Circuit-Digest/MLX90640-Thermal-Camera/Images/PCB White BG.png

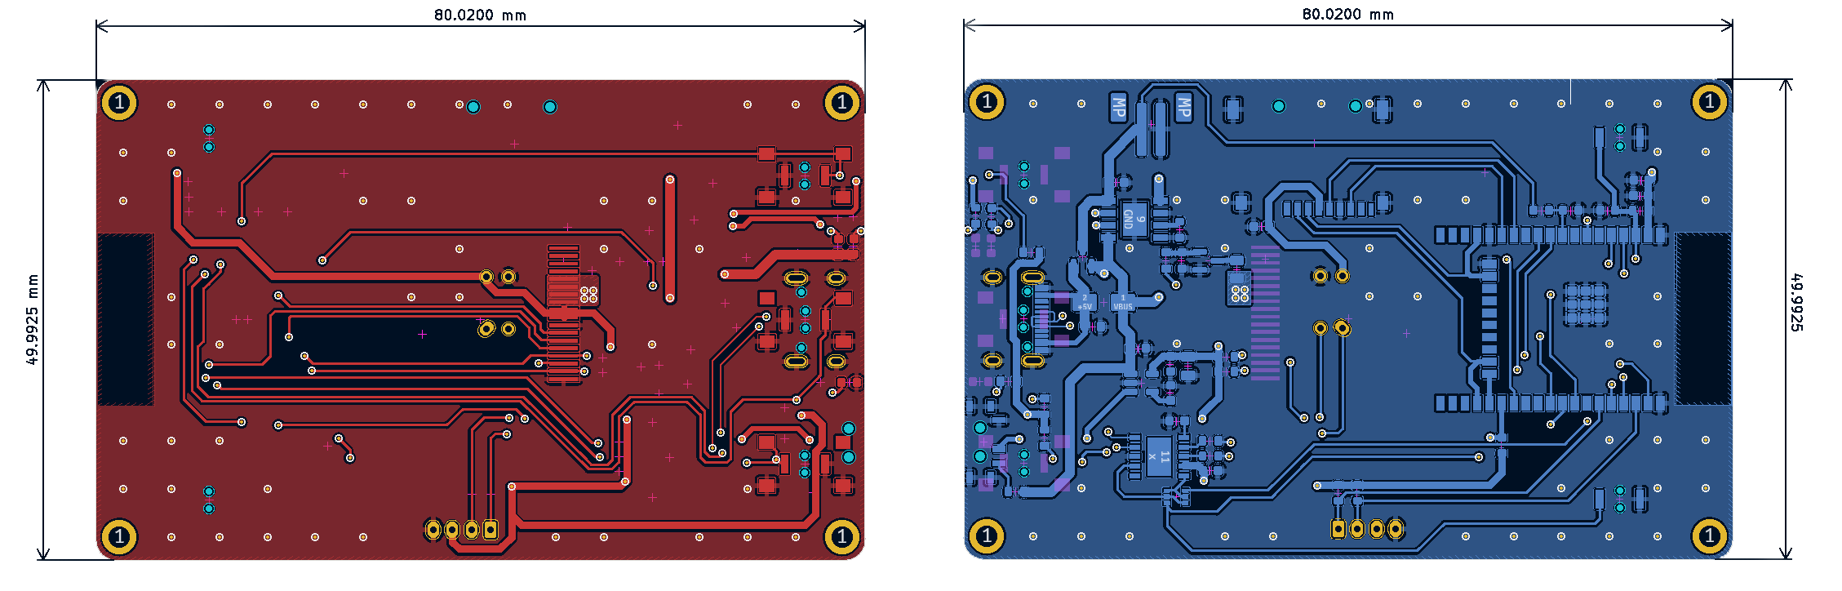
Images/PCB White BG.png
