Circuit-Digest/MLX90640-Thermal-Camera/Thermal_Camera/Error.h

/*
 * Project Name: MLX90640 Thermal Camera
 * Project Brief: Firmware for Thermal camera built around ESP32 and MLX90640
 * Author: Jobit Joseph
 * Copyright © Jobit Joseph
 * Copyright © Semicon Media Pvt Ltd
 * Copyright © Circuitdigest.com
 * 
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
 */
 //
// Error
// Data size = 30092 bytes
//
// GIF, Compression=LZW, Size: 160 x 160, 8-Bpp
// 29 frames
//
// for non-Arduino builds...
#ifndef PROGMEM
#define PROGMEM
#endif
const uint8_t Error_GIF[] PROGMEM = {
	0x47,0x49,0x46,0x38,0x39,0x61,0xa0,0x00,0xa0,0x00,0xf7,0xff,0x00,0xff,0x7c,0x80,
	0xff,0xda,0xdc,0xff,0xf2,0xf3,0xff,0xff,0xff,0xff,0xf1,0xf2,0x00,0x00,0x00,0xff,
	0xf3,0xf4,0xff,0xf4,0xf5,0xff,0xd9,0xdb,0xff,0xf0,0xf1,0xff,0xd8,0xda,0xff,0xf6,
	0xf7,0xff,0x7d,0x81,0xff,0xf7,0xf8,0xff,0xd6,0xd8,0xff,0xf5,0xf6,0xff,0xd5,0xd7,
	0xff,0xdb,0xdd,0xff,0xd7,0xd9,0xff,0xf0,0xf2,0xff,0xf7,0xf7,0xff,0xf4,0xf4,0xff,
	0xf6,0xf6,0xff,0x7a,0x7e,0xff,0xdd,0xdf,0xff,0xdc,0xde,0xff,0xf1,0xf3,0xff,0x81,
	0x85,0xff,0xf5,0xf5,0x42,0x38,0x38,0xff,0xe7,0xe9,0xff,0xa9,0xac,0xff,0xa1,0xa4,
	0xff,0x90,0x94,0xff,0x72,0x76,0xff,0xec,0xee,0xff,0x76,0x7a,0xff,0xdf,0xe1,0xff,
	0x79,0x7d,0xff,0xee,0xf0,0xff,0x6d,0x71,0xff,0x6e,0x72,0xff,0x7e,0x82,0xff,0xe1,
	0xe3,0xff,0xec,0xec,0xff,0x89,0x8d,0xff,0xde,0xe0,0xff,0xe6,0xe8,0xd1,0xb1,0xb3,
	0xff,0x74,0x78,0xff,0xad,0xb0,0xff,0x6c,0x70,0xff,0x8d,0x91,0xff,0xe0,0xe2,0xff,
	0xe6,0xe6,0xff,0xf8,0xf8,0xff,0xea,0xeb,0xff,0xe3,0xe5,0xff,0x6d,0x72,0xb8,0xae,
	0xaf,0x9c,0x84,0x86,0xff,0xee,0xee,0xff,0x85,0x89,0xff,0x66,0x6a,0x26,0x0d,0x0e,
	0xff,0x7b,0x7f,0xff,0xeb,0xed,0xff,0x75,0x79,0xff,0xe8,0xea,0xff,0x78,0x7c,0xff,
	0xe4,0xe6,0xff,0x68,0x6c,0xff,0xed,0xef,0xff,0xd5,0xd8,0x42,0x1b,0x1c,0xff,0xa5,
	0xa8,0xff,0x99,0x9d,0xff,0xe2,0xe4,0xff,0xed,0xee,0xff,0x71,0x75,0xff,0xe5,0xe7,
	0xff,0xeb,0xec,0xff,0x95,0x99,0xff,0x69,0x6d,0xff,0x68,0x6d,0x6b,0x30,0x32,0xff,
	0x6a,0x6e,0xff,0xe8,0xe8,0xff,0xd6,0xd9,0xaa,0x50,0x53,0xff,0xf3,0xf3,0xff,0xb6,
	0xb8,0xe9,0xc7,0xc9,0xff,0xd7,0xda,0xff,0xe9,0xea,0xe9,0x71,0x74,0xff,0xe5,0xe6,
	0xd1,0xc6,0xc7,0xff,0xea,0xec,0xff,0xc2,0xc4,0xff,0x70,0x74,0xff,0xe7,0xe8,0xff,
	0x9e,0xa1,0xff,0x68,0x6e,0xff,0x67,0x6c,0x58,0x26,0x28,0xff,0xc5,0xc8,0x6b,0x5a,
	0x5b,0xff,0xf2,0xf2,0xdd,0x6b,0x6e,0xff,0xe9,0xeb,0xff,0xf9,0xf9,0xc5,0xb8,0xb9,
	0x8d,0x41,0x44,0xf4,0x76,0x7a,0xb8,0x57,0x5a,0xff,0xd9,0xdc,0xff,0x6b,0x6f,0x26,
	0x24,0x24,0xaa,0x91,0x92,0x7d,0x39,0x3b,0xff,0xca,0xcc,0xff,0xd1,0xd4,0xff,0x6a,
	0x6f,0xff,0xdf,0xe0,0xff,0x6c,0x71,0xff,0xe1,0xe2,0x9c,0x49,0x4c,0xff,0x64,0x69,
	0x8d,0x77,0x79,0xff,0xb1,0xb4,0xff,0x7f,0x83,0xff,0x6b,0x70,0xff,0xba,0xbc,0xb8,
	0x9d,0x9e,0xff,0xaf,0xb2,0xff,0x74,0x79,0xff,0xab,0xae,0xff,0xe4,0xe5,0xff,0xde,
	0xdf,0xff,0xa8,0xab,0xc5,0x5e,0x61,0xff,0xbe,0xc1,0xff,0xd8,0xdb,0x26,0x1f,0x20,
	0xff,0xfa,0xfa,0xff,0xe3,0xe4,0xff,0xdb,0xdc,0xff,0xf1,0xf1,0xff,0x6f,0x73,0xff,
	0xc8,0xca,0xff,0xf0,0xf0,0xff,0xc3,0xc6,0xc5,0xa7,0xa9,0xff,0x64,0x6a,0xff,0xc0,
	0xc2,0xff,0xf3,0xf5,0xff,0xcc,0xce,0xff,0xdd,0xde,0xff,0xb8,0xba,0xff,0xd0,0xd2,
	0xff,0xda,0xdb,0xff,0xbc,0xbe,0xff,0xf9,0xfa,0xff,0xe2,0xe3,0xff,0xdc,0xdd,0xaa,
	0xa1,0xa2,0xf4,0xd1,0xd2,0xff,0xf2,0xf4,0xff,0xb4,0xb6,0xff,0xf8,0xf9,0xff,0x7d,
	0x80,0xff,0xa0,0xa3,0xff,0x7e,0x81,0xff,0x71,0x76,0x6b,0x65,0x66,0xd1,0x64,0x68,
	0xff,0xce,0xd0,0x58,0x4a,0x4a,0xff,0x75,0x7a,0xff,0x63,0x68,0xdd,0xd2,0xd3,0xff,
	0xd4,0xd6,0xff,0x73,0x77,0xff,0xdb,0xde,0x58,0x53,0x53,0xff,0x70,0x75,0xff,0xe0,
	0xe1,0x7d,0x76,0x77,0xff,0xd9,0xda,0xff,0x78,0x7d,0x8d,0x85,0x86,0x9c,0x94,0x94,
	0xf4,0xe9,0xea,0x26,0x1e,0x1f,0xff,0xfe,0xfe,0xff,0xda,0xdd,0xff,0xf4,0xf6,0xff,
	0xd4,0xd7,0xff,0x79,0x7e,0xff,0xd8,0xd9,0xff,0xdc,0xdf,0x7d,0x69,0x6a,0xff,0x83,
	0x87,0xff,0xa3,0xa6,0xff,0x77,0x7b,0xff,0x61,0x66,0xaa,0x8e,0x8f,0xff,0xd7,0xd8,
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
