Circuit-Digest/MLX90640-Thermal-Camera/Thermal_Camera/success.h

/*
 * Project Name: MLX90640 Thermal Camera
 * Project Brief: Firmware for Thermal camera built around ESP32 and MLX90640
 * Author: Jobit Joseph
 * Copyright © Jobit Joseph
 * Copyright © Semicon Media Pvt Ltd
 * Copyright © Circuitdigest.com
 * 
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
 */
 //
// success
// Data size = 62287 bytes
//
// GIF, Compression=LZW, Size: 160 x 160, 8-Bpp
// 19 frames
//
// for non-Arduino builds...
#ifndef PROGMEM
#define PROGMEM
#endif
const uint8_t success_GIF[] PROGMEM = {
	0x47,0x49,0x46,0x38,0x39,0x61,0xa0,0x00,0xa0,0x00,0xf7,0xff,0x00,0x3b,0xc2,0x3c,
	0x69,0xe4,0x6a,0xff,0xff,0xff,0x6a,0xe5,0x6b,0x37,0xbf,0x38,0x6e,0xe8,0x6f,0x36,
	0xbe,0x37,0x6c,0xe6,0x6d,0x6d,0xe7,0x6e,0x38,0xc0,0x39,0x3a,0xc1,0x3b,0x3c,0xc2,
	0x3d,0xa9,0xe0,0xa9,0x65,0xe1,0x66,0x66,0xe2,0x67,0x6e,0xed,0x6c,0x39,0xc1,0x3a,
	0x69,0xe3,0x6a,0xf4,0xfb,0xf4,0x41,0xc6,0x42,0x70,0xf0,0x6d,0x50,0xd2,0x51,0x68,
	0xe3,0x6a,0x6b,0xe5,0x6c,0x5e,0xd1,0x66,0x9c,0xdc,0x9d,0x54,0xd5,0x55,0x6f,0xee,
	0x6c,0xcc,0xec,0xcc,0x45,0xc9,0x46,0x6c,0xe8,0x6b,0x6f,0xe8,0x70,0x35,0xbe,0x36,
	0x61,0xde,0x62,0x62,0xcb,0x62,0x6b,0xe6,0x6c,0x65,0xdd,0x68,0xd7,0xf0,0xd7,0x6a,
	0xe5,0x6a,0x6c,0xe9,0x6b,0xb5,0xe4,0xb5,0x6b,0xe7,0x6b,0x52,0xbc,0x61,0x3a,0xc2,
	0x3a,0x35,0xc0,0x36,0x60,0xd4,0x66,0xeb,0xf7,0xeb,0x50,0xc6,0x50,0x6e,0xe7,0x6e,
	0x47,0xab,0x5d,0x39,0xc0,0x3a,0x69,0xe5,0x6a,0x36,0xbf,0x37,0x6a,0xe8,0x6b,0x98,
	0xdf,0x99,0x6d,0xea,0x6c,0x59,0xd8,0x5a,0x49,0xcc,0x4a,0xec,0xf9,0xec,0x72,0xf4,
	0x6e,0x6a,0xe4,0x6b,0x29,0xbd,0x2a,0x8f,0xd7,0x8f,0x24,0xbb,0x25,0x6a,0xe6,0x6a,
	0xe1,0xf4,0xe1,0x59,0xca,0x64,0x72,0xcf,0x73,0x6c,0xe7,0x6d,0xdc,0xf4,0xdc,0xce,
	0xf0,0xce,0x4c,0xb2,0x5f,0x67,0xe2,0x68,0x5c,0xda,0x5d,0x6b,0xd1,0x6b,0xc1,0xe8,
	0xc1,0x93,0xdd,0x94,0x3d,0xc3,0x3e,0x52,0xc9,0x53,0x38,0xbf,0x39,0x2c,0xbd,0x2d,
	0x4c,0xce,0x4d,0x30,0xbf,0x31,0x5a,0xcc,0x5c,0x6a,0xe6,0x6b,0x3d,0xc2,0x3e,0x55,
	0xc1,0x62,0x81,0xd3,0x81,0x5c,0xce,0x65,0x36,0xc1,0x37,0x7a,0xd6,0x7b,0x70,0xee,
	0x6d,0xa4,0xe3,0xa4,0x71,0xf2,0x6d,0x43,0xc8,0x44,0x8c,0xdb,0x8c,0x61,0xd7,0x67,
	0x5a,0xd9,0x5b,0x68,0xe2,0x6a,0x3c,0xc3,0x3d,0x5f,0xdc,0x60,0x72,0xf2,0x6d,0x75,
	0xf8,0x6f,0x73,0xf6,0x6e,0x46,0xca,0x47,0xf9,0xfd,0xf9,0x62,0xd9,0x67,0x56,0xc4,
	0x63,0x3e,0xc4,0x3f,0x5d,0xdb,0x5e,0x4b,0xcd,0x4c,0x56,0xd6,0x57,0x83,0xd8,0x83,
	0x7a,0xe8,0x7b,0x23,0xbb,0x24,0x4d,0xd0,0x4e,0x48,0xc6,0x49,0x4e,0xb6,0x5f,0x4f,
	0xd1,0x50,0x5b,0xcc,0x64,0xbb,0xea,0xbb,0x74,0xd4,0x74,0x38,0xc1,0x39,0x35,0xbd,
	0x36,0x68,0xe4,0x69,0x2a,0xbd,0x2b,0x67,0xd0,0x68,0x64,0xe0,0x65,0x26,0xbc,0x27,
	0x6d,0xeb,0x6c,0x53,0xd4,0x54,0x44,0xc5,0x45,0x58,0xd7,0x59,0x6d,0xe6,0x6e,0xf5,
	0xfb,0xf5,0x48,0xcc,0x49,0x63,0xdf,0x64,0x6a,0xe7,0x6b,0x2e,0xbe,0x30,0xf2,0xfb,
	0xf2,0x6d,0xe8,0x6e,0xe5,0xf7,0xe5,0x63,0xda,0x68,0x37,0xbe,0x38,0x58,0xc8,0x63,
	0xc4,0xee,0xc5,0x72,0xf3,0x6e,0x57,0xc6,0x63,0x6b,0xe7,0x6a,0x43,0xc4,0x43,0xd3,
	0xf1,0xd3,0x3b,0xc1,0x3c,0x53,0xd3,0x54,0x6b,0xe6,0x6b,0x33,0xbf,0x34,0x39,0xc2,
	0x3a,0xb4,0xe7,0xb4,0x6a,0xe7,0x6a,0x25,0xbb,0x26,0x22,0xba,0x23,0xaf,0xe6,0xaf,
	0x88,0xdc,0x88,0x6e,0xeb,0x6c,0x6d,0xeb,0x6b,0x34,0xbd,0x35,0x42,0xc7,0x43,0x3e,
	0xc3,0x3f,0x6a,0xe4,0x6a,0x53,0xbf,0x62,0xa8,0xe4,0xa8,0x67,0xe1,0x69,0x6e,0xeb,
	0x6b,0x3a,0xc0,0x3b,0x3b,0xc3,0x3c,0x71,0xf2,0x6e,0x5e,0xcd,0x5f,0x36,0xbd,0x37,
	0x69,0xe6,0x6a,0x6c,0xe5,0x6d,0x68,0xe4,0x6a,0xde,0xf8,0xde,0x4f,0xc8,0x4f,0xfe,
	0xff,0xff,0x6b,0xe6,0x6a,0xa4,0xed,0xa5,0x4d,0xc5,0x4d,0x6e,0xe9,0x6f,0xde,0xf5,
	0xdf,0x69,0xe5,0x6b,0xc1,0xec,0xc2,0xfe,0xff,0xfe,0xc3,0xec,0xc4,0x57,0xc6,0x64,
	0xbf,0xeb,0xbf,0x52,0xd3,0x53,0xef,0xfa,0xef,0x37,0xc1,0x38,0x6e,0xd2,0x6f,0xfb,
	0xfe,0xfb,0x6f,0xef,0x6c,0xd5,0xf0,0xd6,0x12,0xb6,0x13,0x87,0xda,0x87,0xd8,0xf3,
	0xd8,0xb9,0xf1,0xb9,0xff,0xfe,0xff,0xa8,0xde,0xa8,0x71,0xf1,0x6e,0x46,0xc6,0x47,
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
