Circuit-Digest/MLX90640-Thermal-Camera/Thermal_Camera/Open_Sans_ExtraBold_10.h

/*
 * Project Name: MLX90640 Thermal Camera
 * Project Brief: Firmware for Thermal camera built around ESP32 and MLX90640
 * Author: Jobit Joseph
 * Copyright © Jobit Joseph
 * Copyright © Semicon Media Pvt Ltd
 * Copyright © Circuitdigest.com
 * 
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
 */

const uint8_t Open_Sans_ExtraBold_10Bitmaps[] PROGMEM = {

	// Bitmap Data:
	0x00, // ' '
	0xD9,0x20,0x90, // '!'
	0xB6,0x80, // '"'
	0x34,0x59,0xF9,0x4F,0xCD,0x16,0x00, // '#'
	0x11,0xFC,0x38,0x78,0x78,0xFE,0x10, // '$'
	0x76,0x6A,0x37,0x0F,0xE1,0xD8,0xAC,0xDC, // '%'
	0x38,0x68,0x78,0x73,0xDE,0xCE,0x7F, // '&'
	0xE0, // '''
	0x5B,0x69,0xB6,0x40, // '('
	0x4D,0xB2,0xDB,0x40, // ')'
	0x27,0xDC,0xA0, // '*'
	0x31,0xBE,0x63,0x00, // '+'
	0x5C, // ','
	0xFC, // '-'
	0x50, // '.'
	0x33,0x66,0x64,0xC0, // '/'
	0x79,0x2C,0xF3,0xCD,0x27,0x80, // '0'
	0x3B,0xD6,0x31,0x8C,0x60, // '1'
	0x79,0x21,0x86,0x31,0x8F,0xC0, // '2'
	0xF8,0x61,0x9C,0x1C,0x7F,0x80, // '3'
	0x18,0xE7,0x96,0xFC,0x61,0x80, // '4'
	0x79,0x07,0x86,0x0C,0x6F,0x80, // '5'
	0x39,0x07,0xB3,0xCD,0x37,0x80, // '6'
	0xFC,0x61,0x86,0x30,0xC6,0x00, // '7'
	0x79,0x27,0x9C,0xFF,0x37,0x80, // '8'
	0x7B,0x2C,0xDF,0x0C,0x67,0x00, // '9'
	0x51,0x40, // ':'
	0x48,0x04,0xB0, // ';'
	0x0C,0xEC,0x0E,0x0C, // '<'
	0xFC,0x0F,0xC0, // '='
	0xC1,0xC0,0xDC,0xC0, // '>'
	0xF0,0xCC,0xC0,0x31,0x80, // '?'
	0x1E,0x31,0x97,0xDE,0xFF,0x52,0xD9,0x80,0x7C, // '@'
	0x38,0x51,0xB3,0x67,0xD8,0xF1,0x80, // 'A'
	0xFB,0x6D,0xBC,0xDB,0x6F,0x80, // 'B'
	0x3D,0x86,0x30,0x61,0x83,0x80, // 'C'
	0xF3,0x6D,0xB3,0xDB,0x6F,0x00, // 'D'
	0xFC,0xCE,0xCC,0xF0, // 'E'
	0xFC,0xCE,0xCC,0xC0, // 'F'
	0x3D,0x86,0x37,0x65,0x93,0xC0, // 'G'
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
};
const GFXglyph Open_Sans_ExtraBold_10Glyphs[] PROGMEM = {
// bitmapOffset, width, height, xAdvance, xOffset, yOffset
	  {     0,   1,   1,   4,    0,   -1 }, // ' '
	  {     1,   3,   7,   4,    0,   -7 }, // '!'
	  {     4,   3,   3,   6,    1,   -7 }, // '"'
	  {     6,   7,   7,   8,    0,   -7 }, // '#'
	  {    13,   6,   9,   7,    0,   -8 }, // '$'
	  {    20,   9,   7,  10,    0,   -7 }, // '%'
	  {    28,   8,   7,   9,    0,   -7 }, // '&'
	  {    35,   1,   3,   4,    1,   -7 }, // '''
	  {    36,   3,   9,   5,    1,   -7 }, // '('
	  {    40,   3,   9,   5,    0,   -7 }, // ')'
	  {    44,   5,   4,   6,    0,   -7 }, // '*'
	  {    47,   5,   5,   7,    0,   -6 }, // '+'
	  {    51,   2,   3,   4,    0,   -1 }, // ','
	  {    52,   3,   2,   4,    0,   -3 }, // '-'
	  {    53,   2,   2,   4,    0,   -2 }, // '.'
	  {    54,   4,   7,   5,    0,   -7 }, // '/'
	  {    58,   6,   7,   7,    0,   -7 }, // '0'
	  {    64,   5,   7,   7,    0,   -7 }, // '1'
	  {    69,   6,   7,   7,    0,   -7 }, // '2'
	  {    75,   6,   7,   7,    0,   -7 }, // '3'
	  {    81,   6,   7,   7,    0,   -7 }, // '4'
	  {    87,   6,   7,   7,    0,   -7 }, // '5'
	  {    93,   6,   7,   7,    0,   -7 }, // '6'
	  {    99,   6,   7,   7,    0,   -7 }, // '7'
	  {   105,   6,   7,   7,    0,   -7 }, // '8'
	  {   111,   6,   7,   7,    0,   -7 }, // '9'
	  {   117,   2,   5,   4,    0,   -5 }, // ':'
	  {   119,   3,   7,   4,    0,   -5 }, // ';'
	  {   122,   6,   5,   7,    0,   -6 }, // '<'
	  {   126,   6,   3,   7,    0,   -5 }, // '='
	  {   129,   6,   5,   7,    0,   -6 }, // '>'
	  {   133,   5,   7,   6,    0,   -7 }, // '?'
	  {   138,   9,   8,  10,    0,   -7 }, // '@'
	  {   147,   7,   7,   8,    0,   -7 }, // 'A'
	  {   154,   6,   7,   8,    1,   -7 }, // 'B'
	  {   160,   6,   7,   7,    0,   -7 }, // 'C'
	  {   166,   6,   7,   8,    1,   -7 }, // 'D'
	  {   172,   4,   7,   6,    1,   -7 }, // 'E'
	  {   176,   4,   7,   6,    1,   -7 }, // 'F'
	  {   180,   6,   7,   8,    0,   -7 }, // 'G'
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
};
const GFXfont Open_Sans_ExtraBold_10 PROGMEM = {
(uint8_t  *)Open_Sans_ExtraBold_10Bitmaps,(GFXglyph *)Open_Sans_ExtraBold_10Glyphs,0x20, 0x7E, 14};
