Circuit-Digest/MLX90640-Thermal-Camera/Thermal_Camera/Open_Sans_ExtraBold_9.h

/*
 * Project Name: MLX90640 Thermal Camera
 * Project Brief: Firmware for Thermal camera built around ESP32 and MLX90640
 * Author: Jobit Joseph
 * Copyright © Jobit Joseph
 * Copyright © Semicon Media Pvt Ltd
 * Copyright © Circuitdigest.com
 * 
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
 */
const uint8_t Open_Sans_ExtraBold_9Bitmaps[] PROGMEM = {

	// Bitmap Data:
	0x00, // ' '
	0xFD,0x3C, // '!'
	0xB4, // '"'
	0x28,0xAF,0xDE,0xFD,0x45,0x00, // '#'
	0x23,0xF1,0xC7,0x1E,0x7E,0x20, // '$'
	0x66,0x7A,0x3F,0x0D,0x61,0xF8,0xBC,0xCC, // '%'
	0x70,0xB1,0xE3,0xBD,0xDB,0x9F,0x80, // '&'
	0xC0, // '''
	0x5B,0x6D,0xB2, // '('
	0x4D,0xB6,0xDA, // ')'
	0x27,0xDC,0xA0, // '*'
	0x21,0x3E,0x42,0x00, // '+'
	0x5C, // ','
	0xE0, // '-'
	0xF0, // '.'
	0x32,0x26,0x44,0xC0, // '/'
	0x72,0xB7,0xBD,0xA9,0xC0, // '0'
	0x37,0x73,0x33,0x30, // '1'
	0x70,0xC4,0x67,0x33,0xE0, // '2'
	0xF0,0x84,0xC1,0x8F,0xC0, // '3'
	0x31,0x95,0xAF,0x88,0x40, // '4'
	0x72,0x1C,0x31,0x8B,0xC0, // '5'
	0x32,0x3D,0xBD,0xAD,0xC0, // '6'
	0xF8,0x8C,0x62,0x31,0x80, // '7'
	0x76,0xD4,0xED,0xED,0xC0, // '8'
	0x76,0xB6,0xF1,0x89,0xC0, // '9'
	0x51,0x40, // ':'
	0x50,0x5C, // ';'
	0x00,0xD9,0xC1,0x80, // '<'
	0xF8,0x3E, // '='
	0x06,0x0C,0x7C,0x00, // '>'
	0xF0,0xCC,0x40,0x31,0x80, // '?'
	0x3C,0x62,0x5F,0xE7,0xEF,0x5E,0x40,0x3C, // '@'
	0x38,0x51,0xA3,0x67,0xD8,0xB1,0x80, // 'A'
	0xF4,0xA5,0xE9,0xCF,0xC0, // 'B'
	0x3D,0x84,0x30,0x41,0x83,0x80, // 'C'
	0xF2,0x68,0xA3,0x8A,0x6F,0x00, // 'D'
	0xF8,0x8E,0x88,0xF0, // 'E'
	0xF8,0x8E,0x88,0x80, // 'F'
	0x3D,0x84,0x37,0x45,0x93,0xC0, // 'G'
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
};
const GFXglyph Open_Sans_ExtraBold_9Glyphs[] PROGMEM = {
// bitmapOffset, width, height, xAdvance, xOffset, yOffset
	  {     0,   1,   1,   3,    0,   -1 }, // ' '
	  {     1,   2,   7,   4,    0,   -7 }, // '!'
	  {     3,   3,   2,   6,    1,   -7 }, // '"'
	  {     4,   6,   7,   7,    0,   -7 }, // '#'
	  {    10,   5,   9,   6,    0,   -8 }, // '$'
	  {    16,   9,   7,  10,    0,   -7 }, // '%'
	  {    24,   7,   7,   8,    0,   -7 }, // '&'
	  {    31,   1,   2,   4,    1,   -7 }, // '''
	  {    32,   3,   8,   4,    0,   -7 }, // '('
	  {    35,   3,   8,   4,    0,   -7 }, // ')'
	  {    38,   5,   4,   6,    0,   -7 }, // '*'
	  {    41,   5,   5,   6,    0,   -6 }, // '+'
	  {    45,   2,   3,   4,    0,   -1 }, // ','
	  {    46,   3,   1,   4,    0,   -3 }, // '-'
	  {    47,   2,   2,   4,    0,   -2 }, // '.'
	  {    48,   4,   7,   5,    0,   -7 }, // '/'
	  {    52,   5,   7,   6,    0,   -7 }, // '0'
	  {    57,   4,   7,   6,    0,   -7 }, // '1'
	  {    61,   5,   7,   6,    0,   -7 }, // '2'
	  {    66,   5,   7,   6,    0,   -7 }, // '3'
	  {    71,   5,   7,   6,    0,   -7 }, // '4'
	  {    76,   5,   7,   6,    0,   -7 }, // '5'
	  {    81,   5,   7,   6,    0,   -7 }, // '6'
	  {    86,   5,   7,   6,    0,   -7 }, // '7'
	  {    91,   5,   7,   6,    0,   -7 }, // '8'
	  {    96,   5,   7,   6,    0,   -7 }, // '9'
	  {   101,   2,   5,   4,    0,   -5 }, // ':'
	  {   103,   2,   7,   4,    0,   -5 }, // ';'
	  {   105,   5,   5,   6,    0,   -6 }, // '<'
	  {   109,   5,   3,   6,    0,   -5 }, // '='
	  {   111,   5,   5,   6,    0,   -6 }, // '>'
	  {   115,   5,   7,   6,    0,   -7 }, // '?'
	  {   120,   8,   8,   9,    0,   -7 }, // '@'
	  {   128,   7,   7,   8,    0,   -7 }, // 'A'
	  {   135,   5,   7,   7,    1,   -7 }, // 'B'
	  {   140,   6,   7,   7,    0,   -7 }, // 'C'
	  {   146,   6,   7,   8,    1,   -7 }, // 'D'
	  {   152,   4,   7,   6,    1,   -7 }, // 'E'
	  {   156,   4,   7,   6,    1,   -7 }, // 'F'
	  {   160,   6,   7,   8,    0,   -7 }, // 'G'
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
};
const GFXfont Open_Sans_ExtraBold_9 PROGMEM = {
(uint8_t  *)Open_Sans_ExtraBold_9Bitmaps,(GFXglyph *)Open_Sans_ExtraBold_9Glyphs,0x20, 0x7E, 13};
